palette-system/azcard/images/pcb_bottom.png

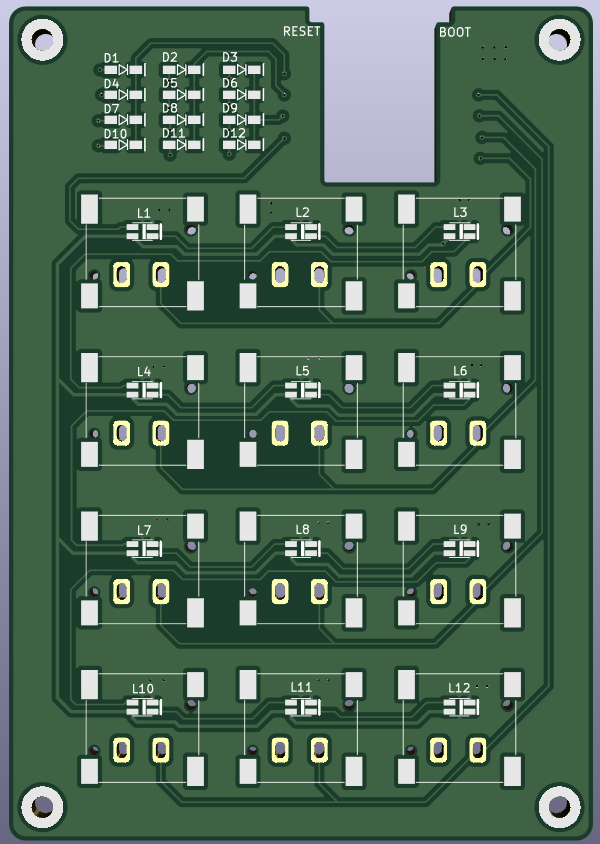
images/pcb_bottom.png
