palette-system/azcard/images/pcb_top.png

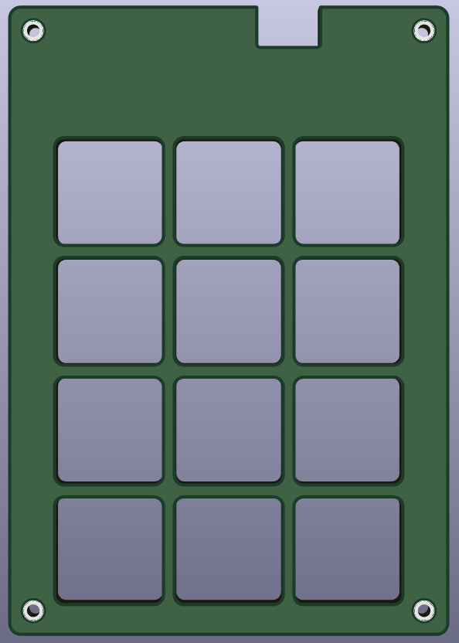
images/pcb_top.png
